gabrielmartinezservili/Graphic-Tool/Graphic tool/3D files (STL)/crown.stl

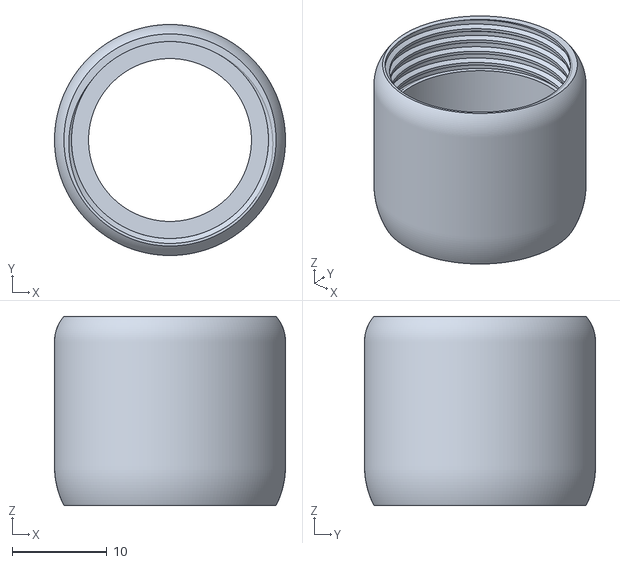
[picture p15: CAD file, 2022-09-20]
Graphic tool/3D files (STL)/crown.stl
24.4 x 24.4 x 20.0
