gabrielmartinezservili/Graphic-Tool/Graphic tool/3D files (STL)/Storage boxes/Cover_tips_box.stl

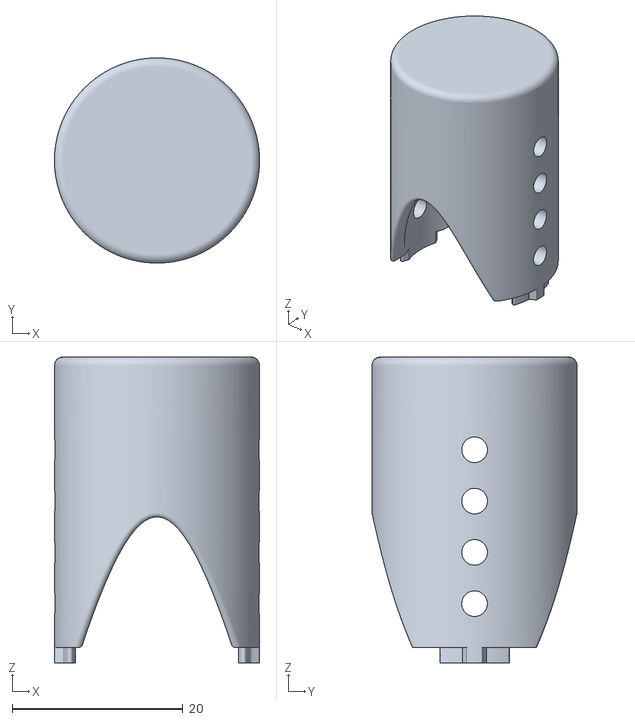
[picture p16: CAD file, 2022-02-28]
Graphic tool/3D files (STL)/Storage boxes/Cover_tips_box.stl
24.0 x 24.0 x 35.8
