gabrielmartinezservili/Graphic-Tool/Graphic tool/3D files (STL)/Tips/Flexible tips (TPE)/example_parameter_flexible_tip.3mf

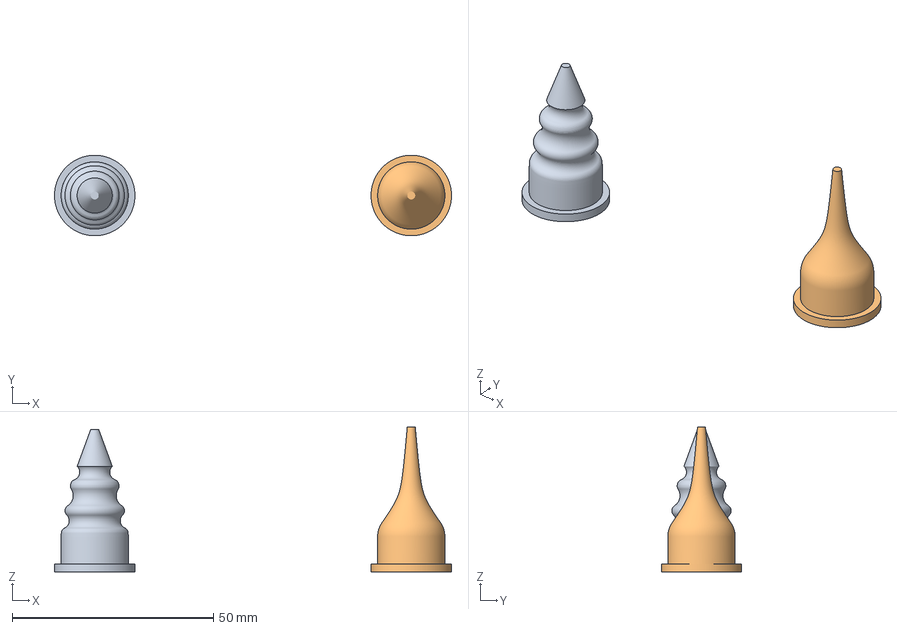
[picture p17: CAD file, 2022-02-28]
Graphic tool/3D files (STL)/Tips/Flexible tips (TPE)/example_parameter_flexible_tip.3mf
98.6 x 20.0 x 36.0 mm
pointe_épaisse
pointe_fine
