gabrielmartinezservili/Graphic-Tool/Graphic tool/3D files (STL)/connector.stl

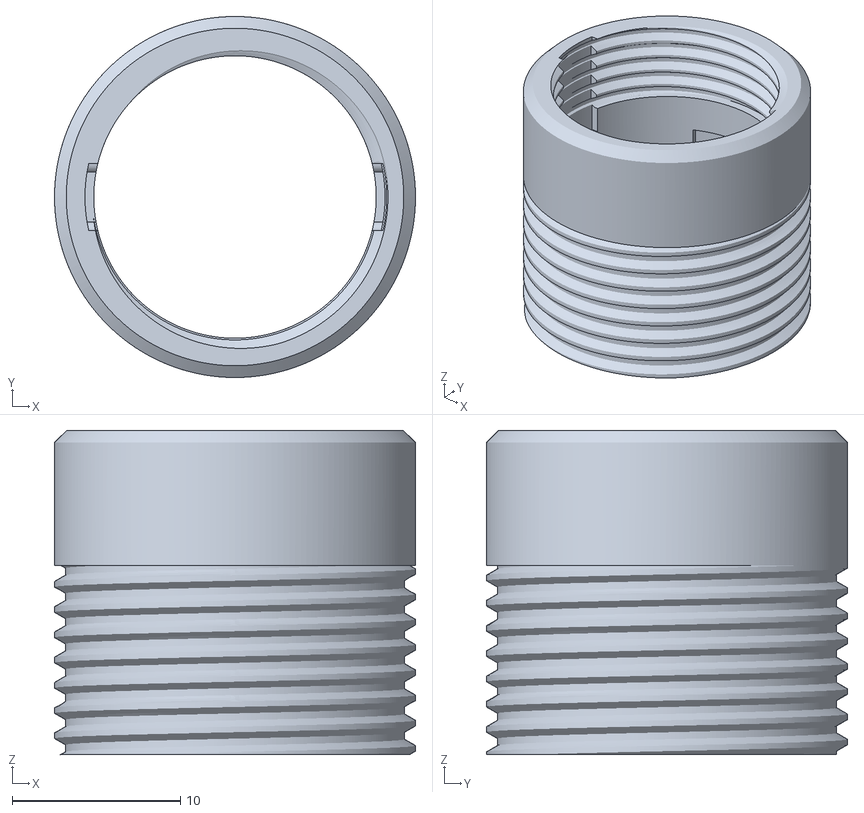
[picture p18: CAD file, 2022-09-20]
Graphic tool/3D files (STL)/connector.stl
21.4 x 21.5 x 19.3
