gabrielmartinezservili/Graphic-Tool/Graphic tool/3D files (STL)/Storage boxes/Cover_shutters_box.stl

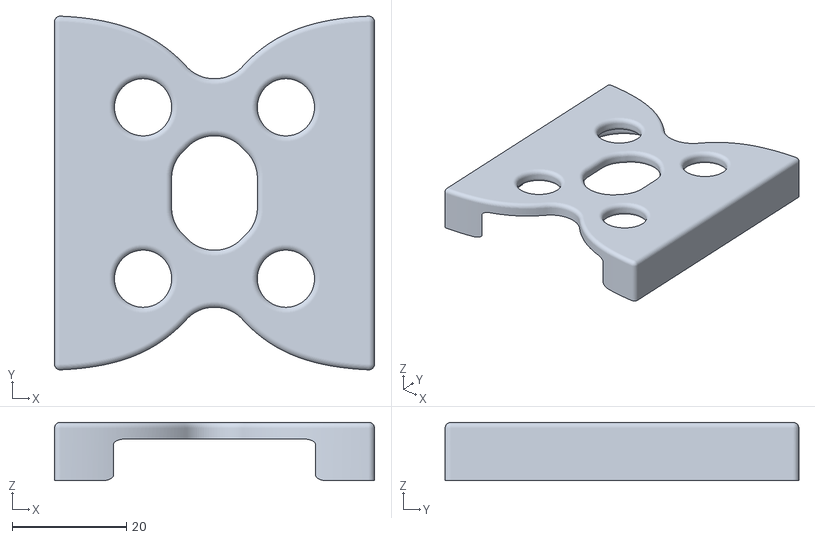
[picture p19: CAD file, 2022-02-28]
Graphic tool/3D files (STL)/Storage boxes/Cover_shutters_box.stl
56.0 x 61.9 x 10.2
