gabrielmartinezservili/Graphic-Tool/Graphic tool/3D files (STL)/Storage boxes/Base_shutters_box.stl

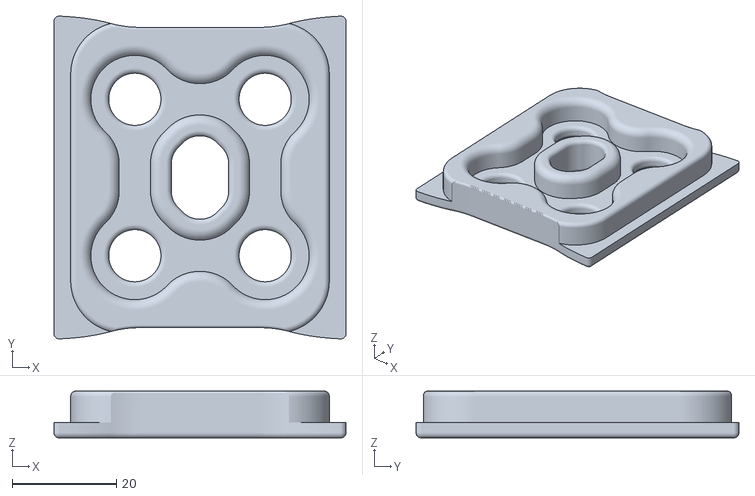
[picture p20: CAD file, 2022-02-28]
Graphic tool/3D files (STL)/Storage boxes/Base_shutters_box.stl
56.0 x 61.9 x 9.00
