gabrielmartinezservili/Graphic-Tool/Graphic tool/3D files (STL)/tank.stl

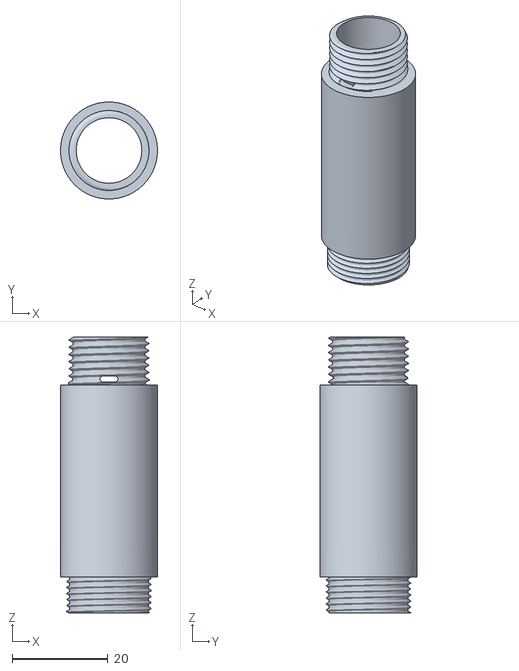
[picture p21: CAD file, 2022-09-20]
Graphic tool/3D files (STL)/tank.stl
20.2 x 20.2 x 57.5
