gabrielmartinezservili/Graphic-Tool/Graphic tool/3D files (STL)/seal_support.stl

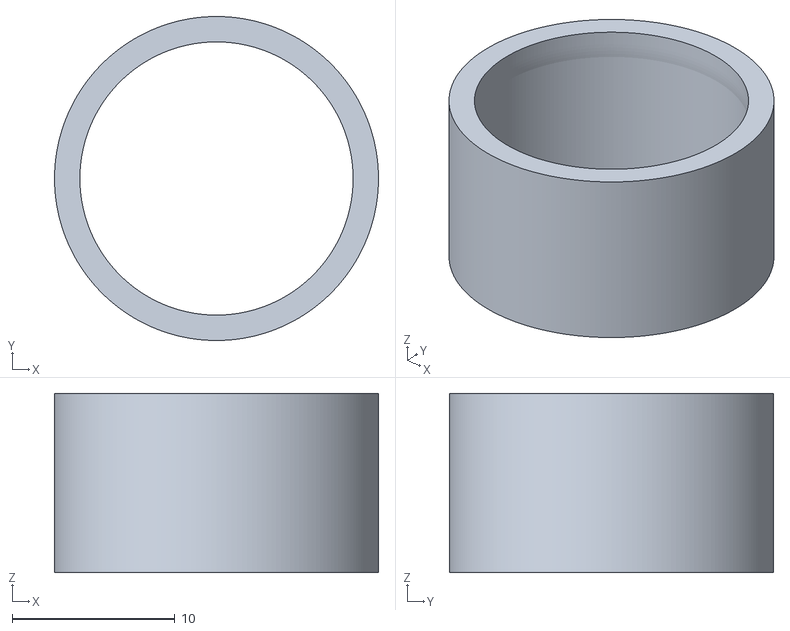
[picture p22: CAD file, 2022-09-20]
Graphic tool/3D files (STL)/seal_support.stl
19.9 x 19.9 x 11.0
