gabrielmartinezservili/Graphic-Tool/Graphic tool/3D files (STL)/cap.stl

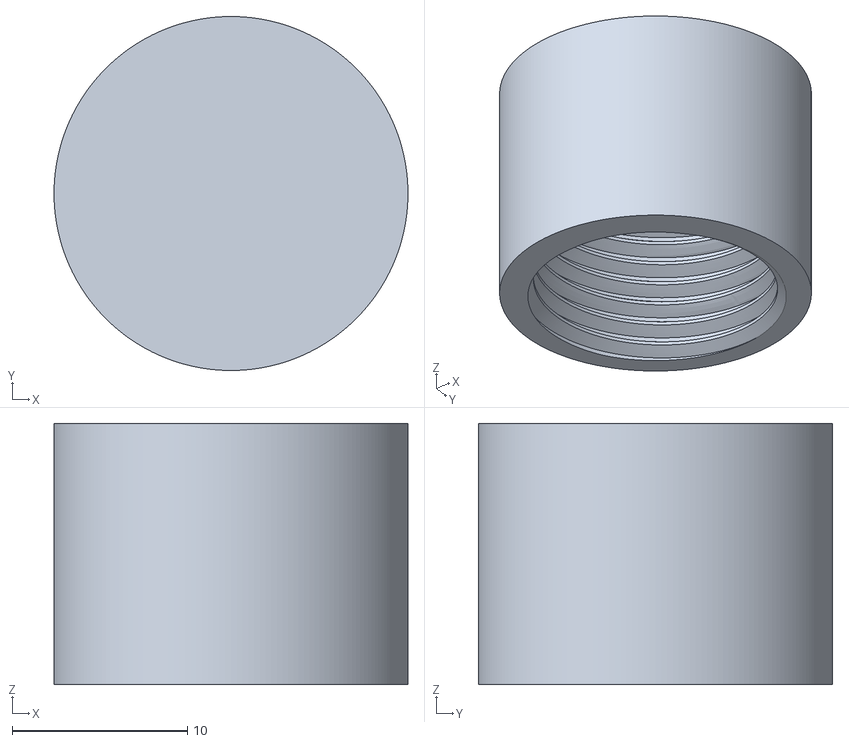
[picture p23: CAD file, 2022-09-20]
Graphic tool/3D files (STL)/cap.stl
20.2 x 20.2 x 14.9
