gabrielmartinezservili/Graphic-Tool/Graphic tool/3D files (STL)/cura_ball_point.3mf

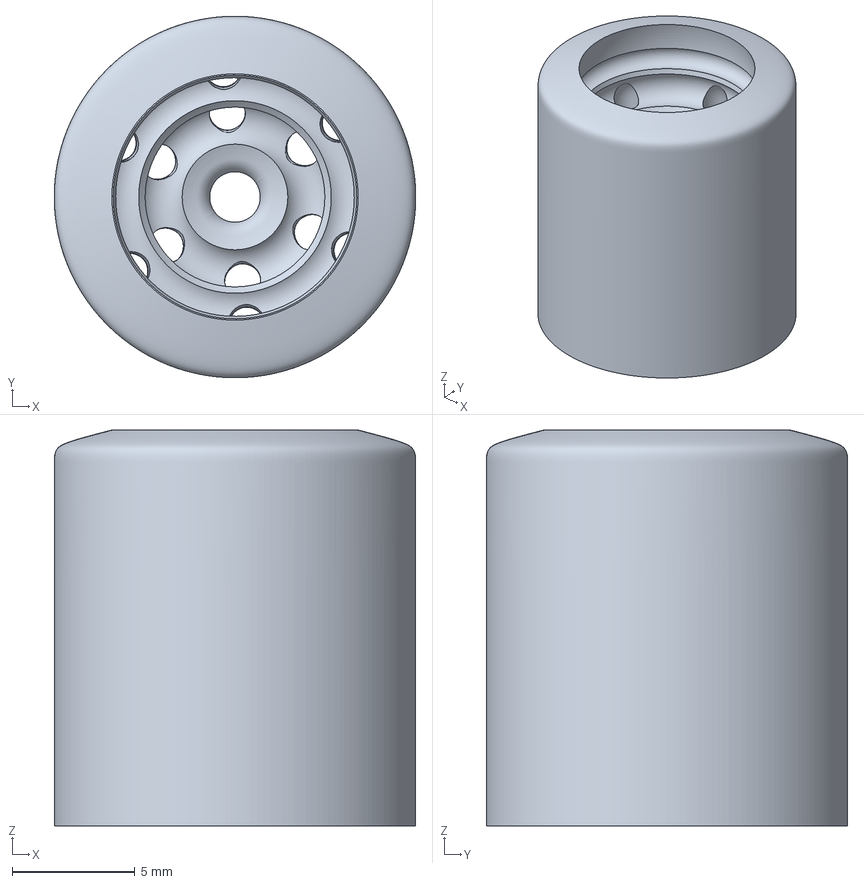
[picture p24: CAD file, 2022-09-20]
Graphic tool/3D files (STL)/cura_ball_point.3mf
14.7 x 14.7 x 16.1 mm
